yomole/TailGator/Simulation/Main PCB/5V Protection Circuits/5V_RPP_Plot.png

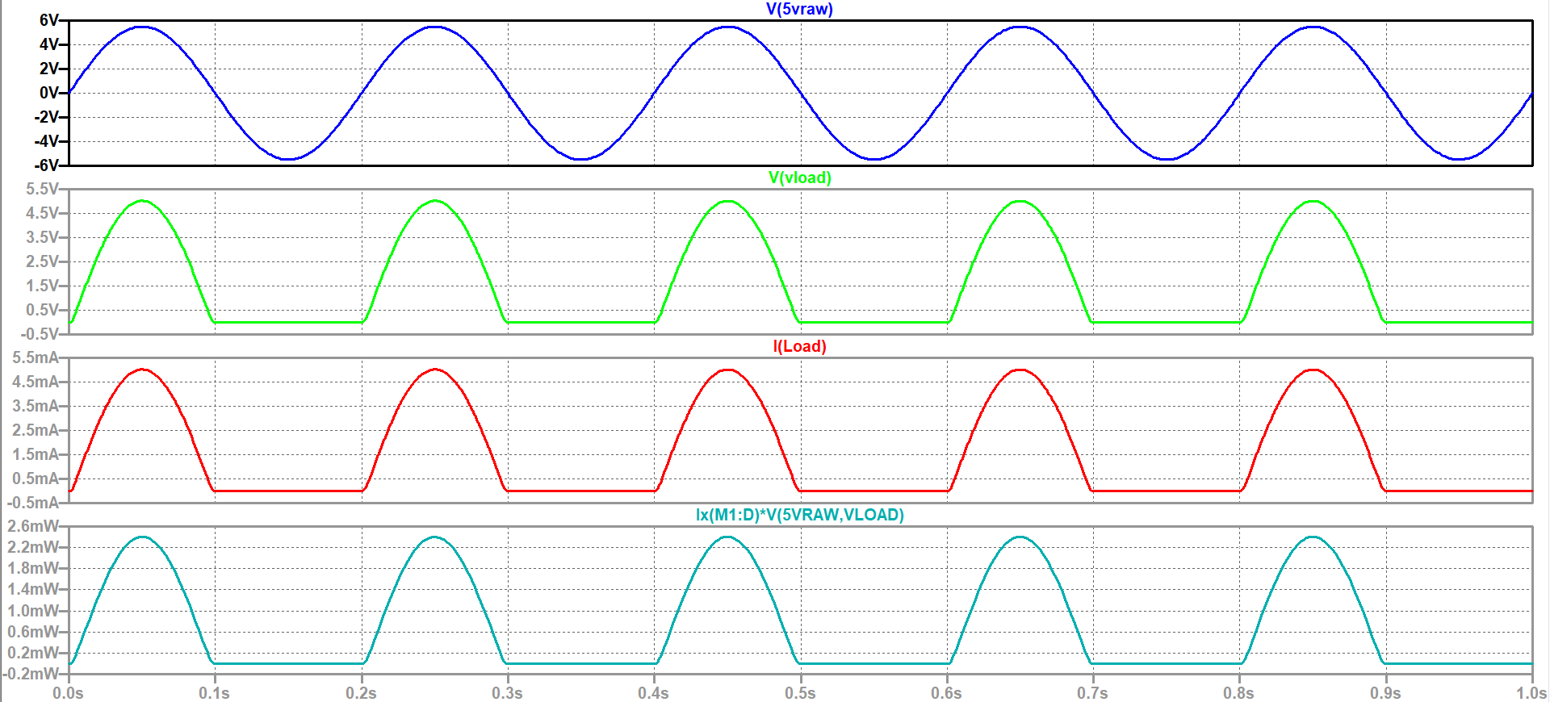
Simulation/Main PCB/5V Protection Circuits/5V_RPP_Plot.png
