yomole/TailGator/Simulation/Main PCB/5V Protection Circuits/Draft1.asc

R1: res; 10k
R2: res; 1k
R3: res; 10k
R4: res; 110
U1: DMP3056L
U2: F2N7002W
V1: voltage; PULSE(0 3.3 100m 10n 10n 100m 200m)
V2: voltage; 5
Named nets: 0
.tran 1
