yomole/TailGator/Simulation/Main PCB/3V3 Protection Circuits/3V3_Protection.asc

C2: cap; 1µF
C3: cap; 100nF
LOAD: res; 10
M2: pmos; AONR21321
R1: res; 3.3k
SCR1: s8006d; TN805-600B
U1: DI_BZT52C4V7; BZT52C3V0
U2: fuse2
V2: voltage; PWL(0 0 50m 0 51m -5.5 100m -5.5 101m -6 150m -6 151m -24 200m -24 201m 3.3 250m 3.3 251m 3.9 300m 3.9 301m 3.9 350m 24)
Named nets: Vd, 3V3RAW, 0, 3V3RPP, 3V3LOAD, VSupply
.tran 400m
REVERSE POLARITY PROTECTION
TAILGATOR INTERCONNECT SYSTEM
PROTECTION CIRCUIT SIMULATION
11/24/2023
AUTHORS:
YOVANY MOLINA
BLAKE SANDERS
DATE:
.lib "SSM3J140TU_PSpice_20200609.lib"
.lib "Zener_DiodesInc.lib"
.lib "st_standard_sensitive_scr.lib"
.lib "fuse2.lib"
SUPPLY
OVERVOLTAGE PROTECTION
TEST LOAD
NOTES:
- FUSE MODEL NOT EXACT.
3/4/2024
LAST MODIFIED:
