yomole/TailGator/Simulation/Main PCB/5V Protection Circuits/5V_Protection.asc

C2: cap; 1µF
C3: cap; 100nF
LOAD: res; 10
M2: pmos; AONR21321
R1: res; 3.3k
SCR1: s8006d; TN805-600B
U1: DI_BZT52C4V7; BZT52C4V7
U2: fuse2
V2: voltage; PWL(0 0 50m 0 51m -5.5 150m -6 151m -6 200m -24 201m -24 250m 5 251m 5 300m 5.6 301m 5.6 350m 24 351m 24)
Named nets: Vd, 5VRAW, 0, 5VRPP, 5VLOAD, VSupply
.tran 700m
REVERSE POLARITY PROTECTION
.lib "Zener_DiodesInc.lib"
.lib "st_standard_sensitive_scr.lib"
.lib "fuse2.lib"
SUPPLY
OVERVOLTAGE PROTECTION
TEST LOAD
NOTES:
- FUSE MODEL NOT EXACT.
TAILGATOR INTERCONNECT SYSTEM
PROTECTION CIRCUIT SIMULATION
11/24/2023
AUTHORS:
YOVANY MOLINA
BLAKE SANDERS
DATE:
3/4/2024
LAST MODIFIED:
