yomole/TailGator/Simulation/Main PCB/5V Protection Circuits/OVP.asc

C1: cap; 1µF
C2: cap; 100nF
Load: res; 1k
R1: res; 1k
SCR: s8006d; TN805-600B
U1: fuse2
U2: DI_BZT52C4V7
V1: voltage; PWL(0 0 100m 0 100m 5 400m 5.5 600m 6 1 0)
Named nets: 0, 5VRAW, 5VLOAD, VSupply
.tran 1
.lib "SCR_Sxx06x_Sx_Sxx06x_A.lib"
.lib "st_standard_sensitive_scr.lib"
.lib "fuse2.lib"
SUPPLY
CROWBAR CIRCUIT + LOAD
TAILGATOR INTERCONNECT SYSTEM
OVERVOLTAGE PROTECTION
11/19/2023
AUTHORS:
YOVANY MOLINA
BLAKE SANDERS
DATE:
