yomole/TailGator/Simulation/Main PCB/5V Protection Circuits/RPP.asc

C2: cap; 1µF
LOAD: res; 1k
M1: pmos; PMOS_SSM3J140TU
V1: voltage; SINE(0 5.5 5)
Named nets: Vg, Vs, Vd, 0, 5VRAW
.tran 1
PMOSFET REVERSE POLARITY PROTECTION
TAILGATOR INTERCONNECT SYSTEM
PROTECTION CIRCUIT SIMULATION
11/19/2023
AUTHORS:
YOVANY MOLINA
BLAKE SANDERS
DATE:
SUPPLY
.lib "SSM3J140TU_PSpice_20200609.lib"
