yomole/TailGator/CAN_Demo/CAN_Receive/src/usb_manager.rs

use rp2040_hal as hal;
use usb_device;
use usb_device::{
    bus::UsbBusAllocator,
    device::{UsbDevice, UsbDeviceBuilder, UsbVidPid},
};
use usbd_serial::SerialPort;

pub struct UsbManager {
    device: UsbDevice<'static, hal::usb::UsbBus>,
    serial: SerialPort<'static, hal::usb::UsbBus>,
}

impl UsbManager {
    pub fn new(usb_bus: &'static UsbBusAllocator<hal::usb::UsbBus>) -> Self {
    
        let serial = usbd_serial::SerialPort::new(usb_bus);

        let device = UsbDeviceBuilder::new(usb_bus, UsbVidPid(0x2E8A, 0x000a))
            .manufacturer("Raspberry Pi")
            .product("Pico")
            .serial_number("TEST")
            .device_class(usbd_serial::USB_CLASS_CDC)
            .build();

        UsbManager { device, serial }
    }

    pub unsafe fn interrupt(&mut self) {
        if self.device.poll(&mut [&mut self.serial]) {
            let mut buf = [0u8; 64];
            match self.serial.read(&mut buf) {
                Err(_e) => {
                    // Do nothing
                }
                Ok(_count) => {
                    // Do nothing
                }
            }
        }
    }
}

impl core::fmt::Write for UsbManager {
    fn write_str(&mut self, s: &str) -> core::fmt::Result {
        critical_section::with(|_| {
            // Now interrupts are disabled
            match self.serial.write(s.as_bytes()) {
                Err(_e) => {
                    // Do nothing
                }
                Ok(_) => {
                    // Do nothing
                }
            }
        });
        Ok(())
    }
}
